MechatronixLab/STM32XP/FIRMWARE/STM32XP_PROTOTYPE_BREADBOARD/App/Src/display.c

/*
 * display.c
 *
 *  Created on: May 11, 2024
 *      Author: Eng. André A. M. Araújo
 */

#include "display.h"

// Mechatronix Lab Logo
//
// 	To convert a bitmap to an array, use this website and the following configurations:
// 		http://javl.github.io/image2cpp/
//			Code output format: Arduino code
//			Draw mode: 			Vertical - 1 bit per pixel
//
//	Then, copy array contents from the page to the array:
static const uint8_t MECHATRONIX_LAB_LOGO_64x64[] =
{
		0x00, 0x00, 0x00, 0x00, 0x00, 0x00, 0x00, 0x00, 0x00, 0x00, 0x00, 0x00, 0x00, 0x00, 0x00, 0x00,
			0x00, 0x00, 0x00, 0x00, 0x0e, 0xff, 0xff, 0x0f, 0x0f, 0x0f, 0x0f, 0x0f, 0x0f, 0x0f, 0x0f, 0x0f,
			0x0f, 0x0f, 0x0f, 0x0f, 0x0f, 0x0f, 0x0f, 0x0f, 0x0f, 0xff, 0xff, 0x0e, 0x00, 0x00, 0x00, 0x00,
			0x00, 0x00, 0x00, 0x00, 0x00, 0x00, 0x00, 0x00, 0x00, 0x00, 0x00, 0x00, 0x00, 0x00, 0x00, 0x00,
			0x00, 0x00, 0x00, 0x00, 0x00, 0x00, 0x00, 0x00, 0x00, 0x00, 0x00, 0x00, 0x00, 0x00, 0x00, 0x00,
			0x00, 0x00, 0x00, 0x00, 0xc0, 0xff, 0x7f, 0x00, 0x00, 0x00, 0x00, 0x00, 0x00, 0x00, 0x00, 0x00,
			0x00, 0x00, 0x00, 0x00, 0x00, 0x00, 0x00, 0x00, 0x00, 0x7f, 0xff, 0xc0, 0x00, 0x00, 0x00, 0x00,
			0x00, 0x00, 0x00, 0x00, 0x00, 0x00, 0x00, 0x00, 0x00, 0x00, 0x00, 0x00, 0x00, 0x00, 0x00, 0x00,
			0x00, 0x00, 0x00, 0x00, 0x00, 0x00, 0x00, 0x00, 0x00, 0x00, 0x00, 0x00, 0x00, 0x00, 0x00, 0x80,
			0xc0, 0xf0, 0x3c, 0x0f, 0x03, 0x01, 0x00, 0x00, 0x00, 0xc0, 0xe0, 0xc0, 0x80, 0x00, 0x00, 0x00,
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
//	0x00, 0x00, 0x00, 0x00, 0x00, 0x00, 0x00, 0x00, 0x00, 0x00, 0x00, 0x00, 0x00, 0x00, 0x00, 0x00,
//	0x00, 0xe0, 0xf8, 0x3c, 0x0e, 0x03, 0x03, 0x01, 0x61, 0x30, 0x30, 0x30, 0x30, 0x01, 0x01, 0x03,
//	0x03, 0x86, 0x9e, 0xf8, 0xe0, 0x00, 0x00, 0xfc, 0xfc, 0x00, 0x00, 0x80, 0xc0, 0xc0, 0xc0, 0xc0,
//	0x80, 0x00, 0x00, 0xfc, 0xfc, 0x00, 0x80, 0xc0, 0xc0, 0x00, 0x00, 0xc0, 0xf0, 0xf0, 0xc0, 0xc0,
//	0x00, 0x00, 0x80, 0xc0, 0xc0, 0xc0, 0xc0, 0x80, 0x00, 0x00, 0xc0, 0xc0, 0x80, 0xc0, 0x40, 0x00,
//	0x00, 0x07, 0x1f, 0x3c, 0x70, 0xc0, 0xc0, 0x80, 0x80, 0x04, 0x0e, 0x0e, 0x0e, 0x8f, 0x87, 0x87,
//	0xc3, 0xe1, 0x79, 0x1f, 0x07, 0x00, 0x00, 0x3f, 0x3f, 0x00, 0x06, 0x0f, 0x1e, 0x32, 0x32, 0x12,
//	0x1b, 0x02, 0x00, 0x3f, 0x3f, 0x07, 0x0f, 0x3d, 0x30, 0x00, 0x00, 0x00, 0x1f, 0x3f, 0x30, 0x10,
//	0x00, 0x07, 0x1f, 0x18, 0x30, 0x30, 0x18, 0x1f, 0x07, 0x00, 0x3f, 0x3f, 0x00, 0x00, 0x00, 0x00,
//	0x00, 0x00, 0x00, 0x00, 0x00, 0x00, 0x01, 0x01, 0x01, 0x03, 0x03, 0x03, 0x03, 0x03, 0x01, 0x01,
//	0x00, 0x00, 0x00, 0x00, 0x00, 0x00, 0x00, 0x00, 0x00, 0x00, 0x00, 0x00, 0x00, 0x00, 0x00, 0x00,
//	0x00, 0x00, 0x00, 0x00, 0x00, 0x00, 0x00, 0x00, 0x00, 0x00, 0x00, 0x00, 0x00, 0x00, 0x00, 0x00,
//	0x00, 0x00, 0x00, 0x00, 0x00, 0x00, 0x00, 0x00, 0x00, 0x00, 0x00, 0x00, 0x00, 0x00, 0x00, 0x00
//};

void DISPLAY_Init(void)
{
	uint16_t dt = 1000;

	char display_buffer[16];

	OLED_Init();
	OLED_SetCursor(0, 0);

	GFX_DrawLogo( 0, 0,64,64, (uint8_t *) MECHATRONIX_LAB_LOGO_64x64);
	OLED_SetCursor(67, 0);
	GFX_DrawString((uint8_t *)GFX_font_5x7, "  STM32   ");
	OLED_SetCursor(67, 1);
	GFX_DrawString((uint8_t *)GFX_font_5x7, " EXPLORER ");
	OLED_SetCursor(67, 2);
	GFX_DrawString((uint8_t *)GFX_font_5x7, "  BOARD   ");
	OLED_SetCursor(67, 6);
	GFX_DrawString((uint8_t *)GFX_font_5x7, "ENG. ANDRE");
	OLED_SetCursor(67, 7);
	GFX_DrawString((uint8_t *)GFX_font_5x7, "A.M.ARAUJO");

	HAL_Delay(dt);

	sprintf(display_buffer, "V: %d.%d.%d  ", V_MAJOR, V_MINOR, V_PATCH);

	OLED_SetCursor(67, 0);
	GFX_DrawString((uint8_t *)GFX_font_5x7, "STM32XP R0");
	OLED_SetCursor(67, 1);
	GFX_DrawString((uint8_t *)GFX_font_5x7, display_buffer); // Version

	sprintf(display_buffer, "%4d.%02d.%02d  ", version_year, version_month, version_day);
	OLED_SetCursor(67, 2);
	GFX_DrawString((uint8_t *)GFX_font_5x7, display_buffer);

	HAL_Delay(dt);

	OLED_SetCursor(67, 1);
	GFX_DrawString((uint8_t *)GFX_font_5x7, "           ");
	OLED_SetCursor(67, 2);
	GFX_DrawString((uint8_t *)GFX_font_5x7, "           ");
	OLED_SetCursor(67, 3);
	GFX_DrawString((uint8_t *)GFX_font_5x7, "           ");
	OLED_SetCursor(67, 4);
	GFX_DrawString((uint8_t *)GFX_font_5x7, "           ");
	OLED_SetCursor(67, 5);
	GFX_DrawString((uint8_t *)GFX_font_5x7, "           ");

//	OLED_Clear();
}
