MechatronixLab/STM32XP/FIRMWARE/STM32XP_PROTOTYPE_BREADBOARD/App/Src/graphics.c

/*
 * graphics.c
 *
 *  Created on: May 11, 2024
 *      Author: Eng. André A. M. Araújo
 */

#include "graphics.h"

// TODO: Rework functions to use frame buffer

uint8_t GFX_frame_buffer[FRAME_BUFFER_SIZE] = {0};

// 5x7 font:
// 	Source: https://lexus2k.github.io/ssd1306/ssd1306__fonts_8c_source.html
const uint8_t GFX_font_5x7[] =
{
	0x00, 0x05, 0x07, 0x20,

	0x00, 0x00, 0x00, 0x00, 0x00, // sp
	0x00, 0x00, 0x5F, 0x00, 0x00, // !
	0x00, 0x03, 0x00, 0x03, 0x00, // "
	0x14, 0x3E, 0x14, 0x3E, 0x14, // #
	0x24, 0x2A, 0x7F, 0x2A, 0x12, // $
	0x43, 0x33, 0x08, 0x66, 0x61, // %
	0x36, 0x49, 0x55, 0x22, 0x50, // &
	0x00, 0x05, 0x03, 0x00, 0x00, // '
	0x00, 0x1C, 0x22, 0x41, 0x00, // (
	0x00, 0x41, 0x22, 0x1C, 0x00, // )
	0x14, 0x08, 0x3E, 0x08, 0x14, // *
	0x08, 0x08, 0x3E, 0x08, 0x08, // +
	0x00, 0x50, 0x30, 0x00, 0x00, // ,
	0x08, 0x08, 0x08, 0x08, 0x08, // -
	0x00, 0x60, 0x60, 0x00, 0x00, // .
	0x20, 0x10, 0x08, 0x04, 0x02, // /
	0x3E, 0x51, 0x49, 0x45, 0x3E, // 0
	0x00, 0x04, 0x02, 0x7F, 0x00, // 1
	0x42, 0x61, 0x51, 0x49, 0x46, // 2
	0x22, 0x41, 0x49, 0x49, 0x36, // 3
	0x18, 0x14, 0x12, 0x7F, 0x10, // 4
	0x27, 0x45, 0x45, 0x45, 0x39, // 5
	0x3E, 0x49, 0x49, 0x49, 0x32, // 6
	0x01, 0x01, 0x71, 0x09, 0x07, // 7
	0x36, 0x49, 0x49, 0x49, 0x36, // 8
	0x26, 0x49, 0x49, 0x49, 0x3E, // 9
	0x00, 0x36, 0x36, 0x00, 0x00, // :
	0x00, 0x56, 0x36, 0x00, 0x00, // ;
	0x08, 0x14, 0x22, 0x41, 0x00, // <
	0x14, 0x14, 0x14, 0x14, 0x14, // =
	0x00, 0x41, 0x22, 0x14, 0x08, // >
	0x02, 0x01, 0x51, 0x09, 0x06, // ?
	0x3E, 0x41, 0x59, 0x55, 0x5E, // @
	0x7E, 0x09, 0x09, 0x09, 0x7E, // A
	0x7F, 0x49, 0x49, 0x49, 0x36, // B
	0x3E, 0x41, 0x41, 0x41, 0x22, // C
	0x7F, 0x41, 0x41, 0x41, 0x3E, // D
	0x7F, 0x49, 0x49, 0x49, 0x41, // E
	0x7F, 0x09, 0x09, 0x09, 0x01, // F
	0x3E, 0x41, 0x41, 0x49, 0x3A, // G
	0x7F, 0x08, 0x08, 0x08, 0x7F, // H
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
	0x0E, 0x11, 0x11, 0x11, 0x0E, // Degree symbol ° (DEL: \177 = 127 in octal)

	0x00	// This byte is required for italic type of font
};



void GFX_ClearFrame(uint8_t * frame_buffer)
{
	uint16_t i = 0;

	for (i = 0; i < FRAME_BUFFER_SIZE; i++)
	{
		frame_buffer[i] = 0;
	}
}

void GFX_DrawChar(uint8_t * font, uint8_t character)
{
	uint16_t column	= 0;

	for (column = 0; column < 5; column++)
	{
		OLED_SendData(font[(character - 0x20)*5 + column + 0x04]);
	}
	OLED_SendData(0x00);	// Add a blank column at the end of each character
}

void GFX_DrawString(uint8_t * font, char * string)
{
	uint8_t index	= 0;

	while(string[index] != '\0')
	{
		GFX_DrawChar(font, string[index]);
		index++;
	}
}

void GFX_DrawLogo(uint8_t c0, uint8_t p0, uint8_t w, uint8_t h, uint8_t * logo)
{
	uint8_t page 	= 0;
	uint16_t column = 0;
	uint16_t pixel 	= 0;

	for (page = p0 ; page < (p0 + h/8); page++)
	{
		OLED_SetCursor(c0, page);

		for (column = 0; column < w; column++)
		{
			OLED_SendData(logo[pixel++]);
		}
	}
}

void GFX_DrawFrame(uint8_t * frame_buffer)
{
	uint8_t page 	= 0;
	uint16_t column = 0;
	uint16_t sector = 0;

	for (page = 0; page < 8; page++)
	{
		OLED_SetCursor(0, page);

		for (column = 0; column < 128; column++)
		{
			OLED_SendData(frame_buffer[sector++]);
		}
	}
}

void GFX_DrawHalfFrame(uint8_t * frame_buffer)
{
	uint8_t page 	= 0;
	uint8_t column  = 0;
	uint16_t sector = 4 * 128;

	for (page = 4; page < 8; page++)
	{
		OLED_SetCursor(0, page);

		for (column = 0; column < 128; column++)
		{
			OLED_SendData(frame_buffer[sector++]);
		}
	}
}

//void GFX_DrawFrameArea(uint8_t * frame_buffer, uint8_t xi, uint8_t pagei, uint8_t xf, uint8_t pagef)
//{
//	uint8_t page 	= 0;
//	uint8_t column  = 0;
//	uint16_t sector = 0;
//
//	for (page = pagei; page < pagef; page++)
//	{
//		OLED_SetCursor(xi, page);
//
//		for (column = xi; column < xf; column++)
//		{
//			OLED_SendData(frame_buffer[xi + (pagei * 8) + sector++]);
//		}
//	}
//}

void GFX_DrawHorizontalLine	(uint8_t x, uint8_t y, uint8_t dx)
{
	uint8_t counter = 0;

	for (counter = 0; counter < dx; counter++)
	{
		GFX_frame_buffer[x + 128 * (y / 8)] |= 0x01 << (y % 8);
		x++;
	}
}

void GFX_DrawVerticalLine	(uint8_t x, uint8_t y, uint8_t dy)
{
	uint8_t counter = 0;

	for (counter = 0; counter < dy; counter++)
	{
		GFX_frame_buffer[x + 128 * (y / 8)] |= 0x01 << (y % 8);
		y++;
	}
}

void GFX_DrawDiagonalLine	(uint8_t x, uint8_t y, uint8_t dx_dy)
{
	uint8_t counter = 0;

	for (counter = 0; counter < dx_dy; counter++)
	{
		GFX_frame_buffer[x + 128 * (y / 8)] |= 0x01 << (y % 8);
		x++;
		y++;
	}
}

void GFX_DrawLineOctant0	(uint8_t x, uint8_t y, uint8_t dx, uint8_t dy, int8_t x_direction)
{
	int32_t dy2, dy2_dx2, error;

	dy2 = 2*dy;
	dy2_dx2 = dy2 - 2 * dx;
	error = dy2 - (int32_t) dx;

	GFX_frame_buffer[x + 128 * (y / 8)] |= 0x01 << (y % 8);
	while (dx--)
	{
		if (error > 0)
		{
			y++;
			error += dy2_dx2;
		}
		else
		{
			error += dy2;
		}

		x += x_direction;

		GFX_frame_buffer[x + 128 * (y / 8)] |= 0x01 << (y % 8);
	}
}

void GFX_DrawLineOctant1	(uint8_t x, uint8_t y, uint8_t dx, uint8_t dy, int8_t x_direction)
{
	int32_t dx2, dx2_dy2, error;

	dx2 = 2*dx;
	dx2_dy2 = dx2 - 2 * dy;
	error = dx2 - (int32_t) dy;

	GFX_frame_buffer[x + 128 * (y / 8)] |= 0x01 << (y % 8);
	while (dy--)
	{
		if (error > 0)
		{
			x += x_direction;
			error += dx2_dy2;
		}
		else
		{
			error += dx2;
		}

		y++;

		GFX_frame_buffer[x + 128 * (y / 8)] |= 0x01 << (y % 8);
	}
}

void GFX_DrawLine(int8_t x0, int8_t y0, int8_t x1, int8_t y1)
{
	// Based on Bresenham's algorithm. Source:
	// http://www.phatcode.net/res/224/files/html/ch35/35-01.html

	int8_t dx, dy;
	int8_t swap_aux;

	if (y0 > y1)
	{
		swap_aux = y0;
		y0 = y1;
		y1 = swap_aux;

		swap_aux = x0;
		x0 = x1;
		x1 = swap_aux;
	}

	dx = x1 - x0;
	dy = y1 - y0;

	if (dx > 0)
	{
		if (dx > dy)
		{
			GFX_DrawLineOctant0(x0, y0, dx, dy, 1);
		}
		else
		{
			GFX_DrawLineOctant1(x0, y0, dx, dy, 1);
		}
	}
	else
	{
		dx = -dx;

		if (dx > dy)
		{
			GFX_DrawLineOctant0(x0, y0, dx, dy, -1);
		}
		else
		{
			GFX_DrawLineOctant1(x0, y0, dx, dy, -1);
		}
	}
	GFX_DrawFrame(GFX_frame_buffer);

	//GFX_DrawFrameArea(GFX_frame_buffer, x0, (y0 * 8), x1, (y1 * 8));
//	GFX_DrawHalfFrame(GFX_frame_buffer);
}

void GFX_DrawTriangle (int8_t x0, int8_t y0, int8_t x1, int8_t y1, int8_t x2, int8_t y2)
{
	GFX_DrawLine(x0, y0, x1, y1);
	GFX_DrawLine(x1, y1, x2, y2);
	GFX_DrawLine(x2, y2, x0, y0);
}

void GFX_FillRectangle(uint8_t x, uint8_t y, uint8_t dx, uint8_t dy)
{
	uint8_t counter = 0;

	for (counter = 0; counter < dy; counter++)
	{
		GFX_DrawHorizontalLine(x, (y + counter), dx);
	}
	GFX_DrawFrame(GFX_frame_buffer);
}
