MechatronixLab/STM32XP/FIRMWARE/STM32XP_PROTOTYPE_BREADBOARD/App/Inc/isr.h

/*
 * isr.h
 *
 *  Created on: May 12, 2024
 *      Author: Eng. André A. M. Araújo
 */

#ifndef INC_ISR_H_
#define INC_ISR_H_

#include "main.h"
#include "adc.h"
#include "tim.h"

#include "buttons.h"
#include "cli.h"
#include "usb_device_cdc.h"

#define ISR_INTERRUPT_TIMER_HANDLE	htim5
#define ISR_DEBOUNCE_TIMER_HANDLER  htim10

////#define TIM16_SAMPLE_RATE	30					// Hz
//
//#define TIM16_PSC (48000 - 1)					// 1 kHz
//#define TIM16_ARR (1000/TIM16_SAMPLE_RATE - 1)	// TIM16_SAMPLE_RATE Hz

#define ISR_BUTTON_UP		0x01
#define ISR_BUTTON_DOWN		0x02
#define ISR_BUTTON_CENTER	0x04
#define ISR_BUTTON_LEFT		0x08
#define ISR_BUTTON_RIGHT	0x10

extern uint8_t ISR_interrupt_flag;
extern uint8_t ISR_button;

extern volatile uint8_t ISR_flag_data_sent;
extern volatile uint8_t ISR_flag_ADC_EOC;

void ISR_StartInterruptTimer(void);

void HAL_TIM_PeriodElapsedCallback(TIM_HandleTypeDef *htim);

void HAL_GPIO_EXTI_Callback(uint16_t GPIO_Pin);

#endif /* INC_ISR_H_ */
