MechatronixLab/STM32XP/FIRMWARE/STM32XP_PROTOTYPE_BREADBOARD/App/Inc/rtcc.h

/*
 * rtcc.h
 *
 *  Created on: Aug 23, 2024
 *      Author: Eng. André A. M. Araújo
 */

#ifndef INC_RTCC_H_
#define INC_RTCC_H_

#include "rtc.h"

#define RTC_BKUP_DEFINE_CODE 0xFAFAFAFA // qu'est que ce?

void RTCC_Init(void);

#endif /* INC_RTCC_H_ */
