MechatronixLab/STM32XP/FIRMWARE/STM32XP_PROTOTYPE_BREADBOARD/App/Inc/console.h

/*
 * console.h
 *
 *  Created on: May 12, 2024
 *      Author: Eng. André A. M. Araújo
 */

#ifndef INC_CONSOLE_H_
#define INC_CONSOLE_H_

#include <stdio.h>

#include "cli.h"
#include "version.h"

void CONSOLE_Init(void);

#endif /* INC_CONSOLE_H_ */
