MechatronixLab/STM32XP/FIRMWARE/STM32XP_PROTOTYPE_BREADBOARD/App/Inc/display.h

/*
 * display.h
 *
 *  Created on: May 11, 2024
 *      Author: Eng. André A. M. Araújo
 */

#ifndef INC_DISPLAY_H_
#define INC_DISPLAY_H_

#include "oled_ssd1306.h"
#include "graphics.h"

#include "main.h"

#include "version.h"

#include <stdio.h>

void DISPLAY_Init(void);

#endif /* INC_DISPLAY_H_ */
