MechatronixLab/STM32XP/FIRMWARE/STM32XP_PROTOTYPE_BREADBOARD/App/Inc/graphics.h

/*
 * graphics.h
 *
 *  Created on: May 11, 2024
 *      Author: Eng. André A. M. Araújo
 */

#ifndef INC_GRAPHICS_H_
#define INC_GRAPHICS_H_

#include "main.h"

#include "oled_ssd1306.h"

#include <stdlib.h>
#include <string.h>

#define SCREEN_WIDTH		 128
#define SCREEN_HEIGHT	 	  64
#define SCREEN_AREA			(SCREEN_WIDTH * SCREEN_HEIGHT)
#define FRAME_BUFFER_SIZE	(SCREEN_AREA  / 8)

extern uint8_t GFX_frame_buffer[FRAME_BUFFER_SIZE];
extern const uint8_t GFX_font_5x7[];

void GFX_ClearFrame(uint8_t * frame_buffer);

void GFX_DrawChar(uint8_t * font, uint8_t character);
void GFX_DrawString(uint8_t * font, char * string);
void GFX_DrawLogo(uint8_t c0, uint8_t p0, uint8_t w, uint8_t h, uint8_t * logo);
void GFX_DrawFrame(uint8_t * frame_buffer);
void GFX_DrawHalfFrame(uint8_t * frame_buffer);	// TODO: temporary implementation - fix
//void GFX_DrawFrameArea(uint8_t * frame_buffer, uint8_t xi, uint8_t pagei, uint8_t xf, uint8_t pagef);	// TODO: fix

void GFX_DrawHorizontalLine	(uint8_t x, uint8_t y, uint8_t dx);
void GFX_DrawVerticalLine	(uint8_t x, uint8_t y, uint8_t dy);
void GFX_DrawDiagonalLine	(uint8_t x, uint8_t y, uint8_t dx_dy);

void GFX_DrawLineOctant0	(uint8_t x, uint8_t y, uint8_t dx, uint8_t dy, int8_t x_direction);
void GFX_DrawLineOctant1	(uint8_t x, uint8_t y, uint8_t dx, uint8_t dy, int8_t x_direction);

void GFX_DrawLine			(int8_t x0, int8_t y0, int8_t x1, int8_t y1);
void GFX_DrawTriangle 		(int8_t x0, int8_t y0, int8_t x1, int8_t y1, int8_t x2, int8_t y2);

void GFX_DrawCircle			(uint8_t xc, uint8_t yc, uint8_t r);

void GFX_FillRectangle		(uint8_t x, uint8_t y, uint8_t dx, uint8_t dy);

#endif /* INC_GRAPHICS_H_ */
